alfdecapo/EGS_Modell/Bilder/Bodenadapter breit.png

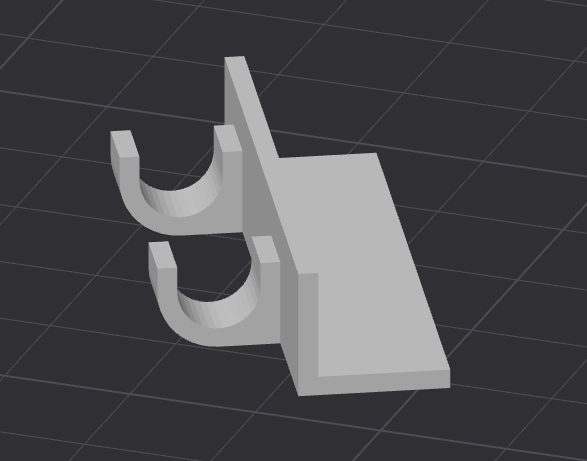
Bilder/Bodenadapter breit.png
