alfdecapo/EGS_Modell/Bilder/Demo_Längs.jpg

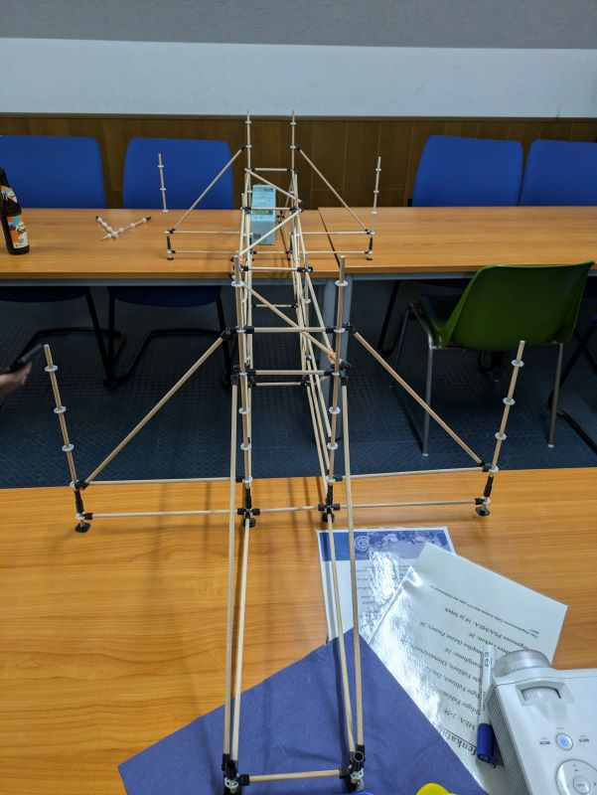
Bilder/Demo_Längs.jpg
