alfdecapo/EGS_Modell/Bilder/Demo_Seite.jpg

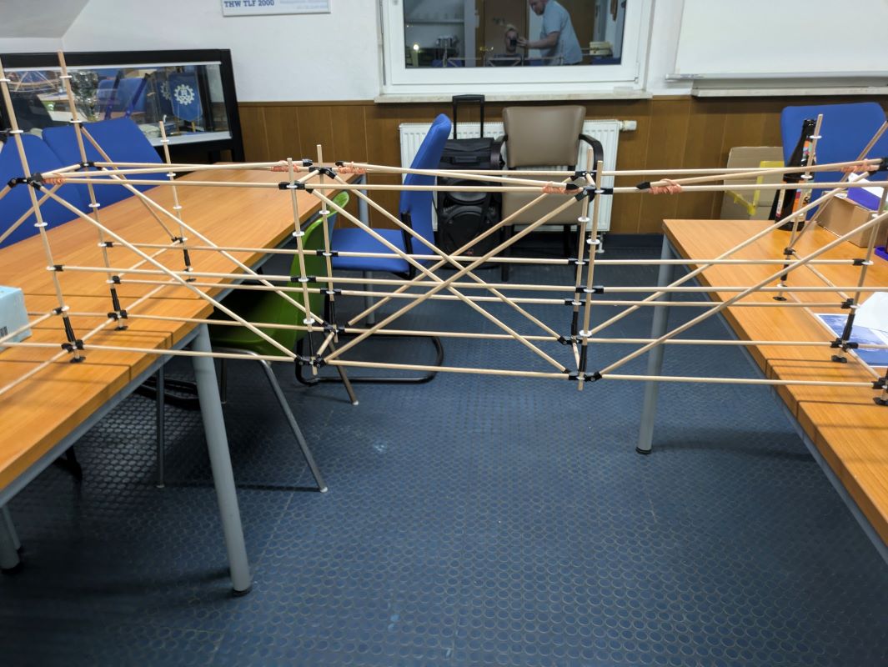
Bilder/Demo_Seite.jpg
