alfdecapo/EGS_Modell/Bilder/Vertikalschablone/Vertikalschablone_MitVertikalstielV2.jpg

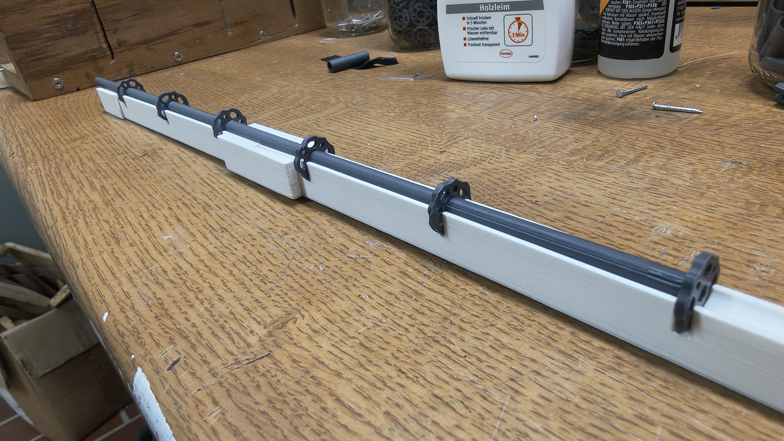
Bilder/Vertikalschablone/Vertikalschablone_MitVertikalstielV2.jpg
