alfdecapo/EGS_Modell/CAD Dateien/Teildruck 7.7/Diagonale Keilschloss.FCStd

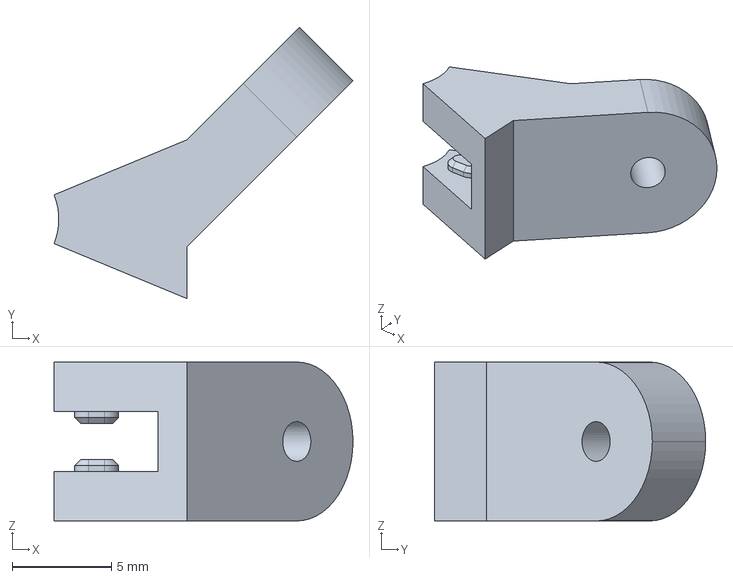
[picture p32: CAD file, 2026-05-11]
CAD Dateien/Teildruck 7.7/Diagonale Keilschloss.FCStd
15.0 x 13.7 x 8.00 mm
