alfdecapo/EGS_Modell/CAD Dateien/Teildruck 7.7/Ursprungsdateien Solid Works/Diagonale Gelenk.SLDPRT

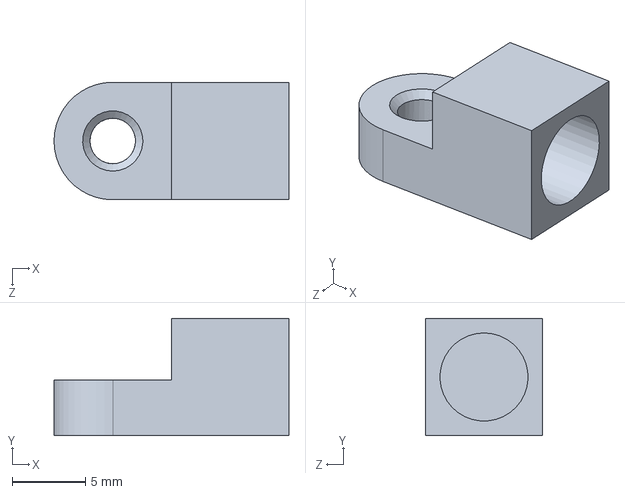
[picture p33: CAD file, 2026-04-20]
CAD Dateien/Teildruck 7.7/Ursprungsdateien Solid Works/Diagonale Gelenk.SLDPRT
16.0 x 8.00 x 8.00 mm
