alfdecapo/EGS_Modell/Drucker Dateien/Teildruck 7.7/Flansch 1zu7.7.STL

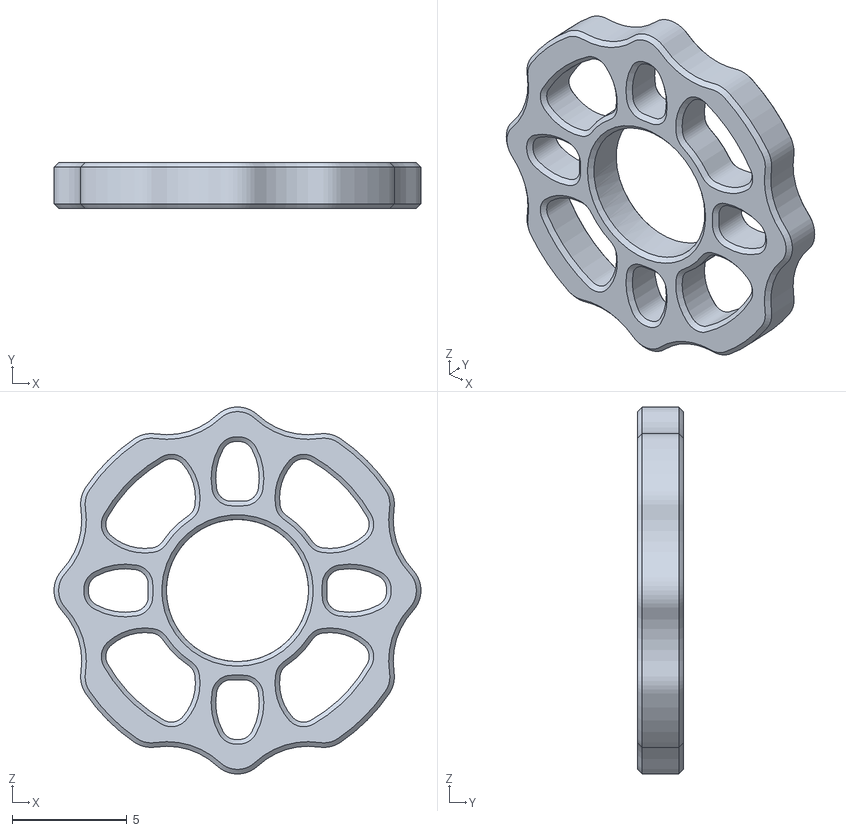
[picture p34: CAD file, 2026-04-20]
Drucker Dateien/Teildruck 7.7/Flansch 1zu7.7.STL
16.0 x 2.00 x 16.0
