alfdecapo/EGS_Modell/CAD Dateien/Teildruck 7.7/Flansch.FCStd

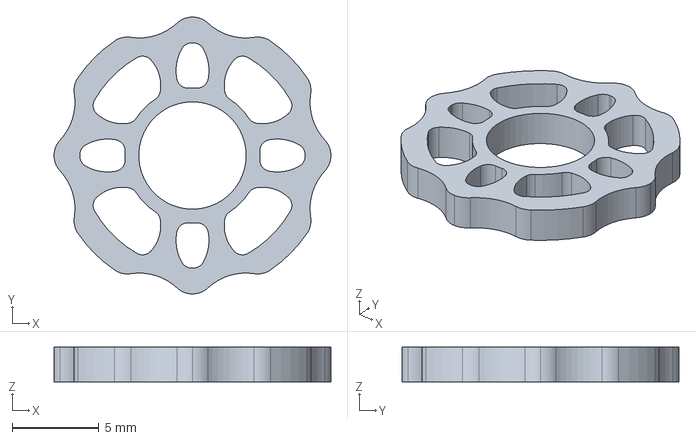
[picture p35: CAD file, 2026-05-11]
CAD Dateien/Teildruck 7.7/Flansch.FCStd
16.0 x 16.0 x 2.00 mm
