alfdecapo/EGS_Modell/Drucker Dateien/Teildruck 7.7/Fußadapter Simpel.STL

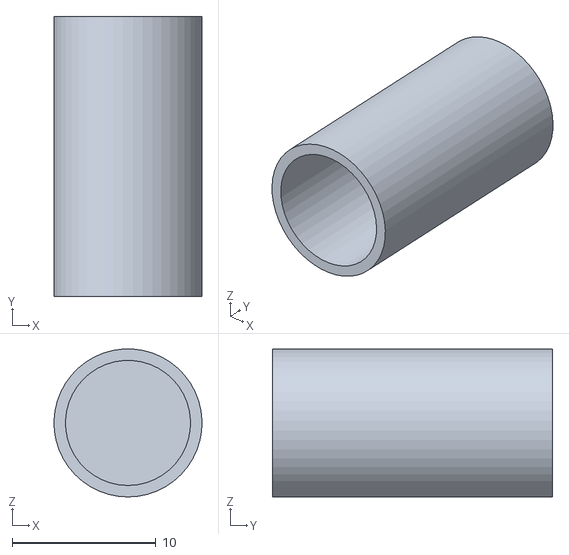
[picture p36: CAD file, 2026-04-20]
Drucker Dateien/Teildruck 7.7/Fußadapter Simpel.STL
10.3 x 19.5 x 10.3
