alfdecapo/EGS_Modell/Drucker Dateien/Teildruck 7.7/Flansch.STL

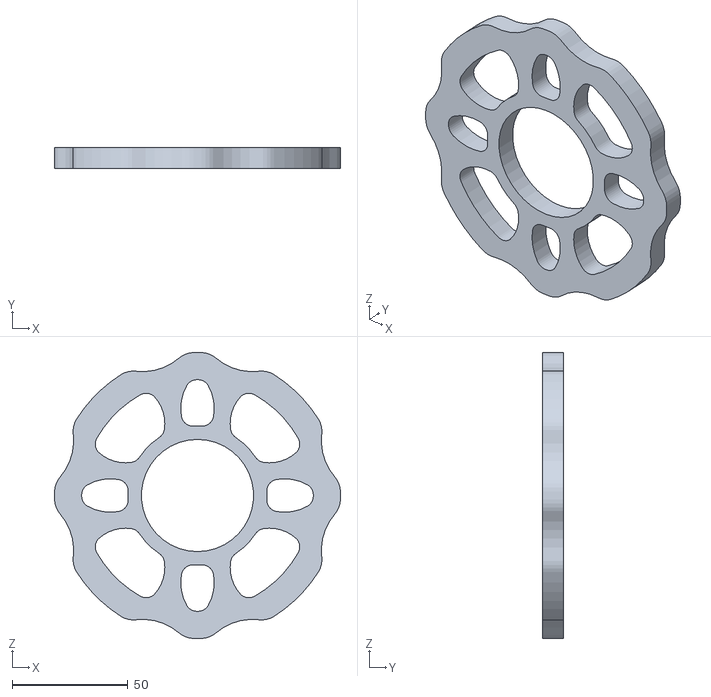
[picture p37: CAD file, 2026-04-20]
Drucker Dateien/Teildruck 7.7/Flansch.STL
123.5 x 9.00 x 123.5
