alfdecapo/EGS_Modell/CAD Dateien/Teildruck 7.7/Horizontale Keilschloss.FCStd

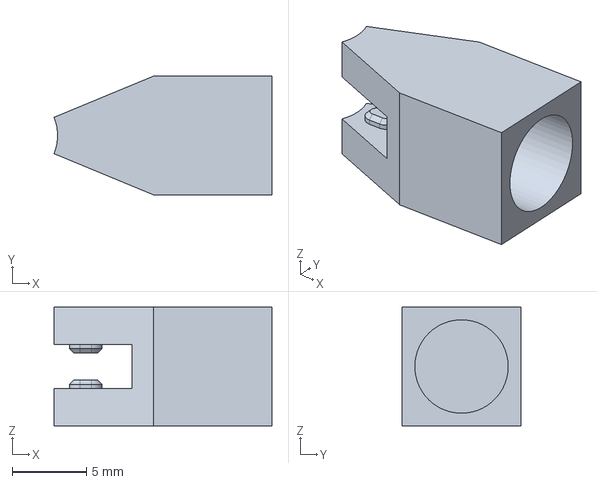
[picture p38: CAD file, 2026-05-11]
CAD Dateien/Teildruck 7.7/Horizontale Keilschloss.FCStd
14.7 x 8.00 x 8.00 mm
