alfdecapo/EGS_Modell/CAD Dateien/Teildruck 7.7/Vertikalen Verbinder.FCStd

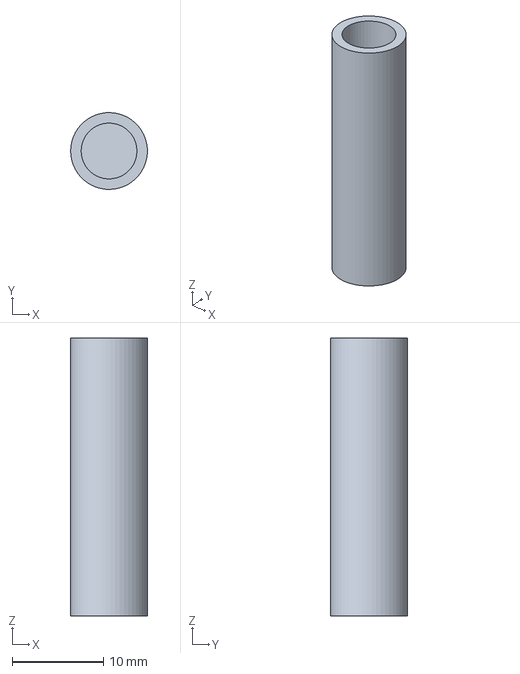
[picture p39: CAD file, 2026-05-11]
CAD Dateien/Teildruck 7.7/Vertikalen Verbinder.FCStd
8.39 x 8.40 x 30.4 mm
