alfdecapo/EGS_Modell/CAD Dateien/Teildruck 7.7/Ursprungsdateien Solid Works/Flansch 1zu7.7.SLDPRT

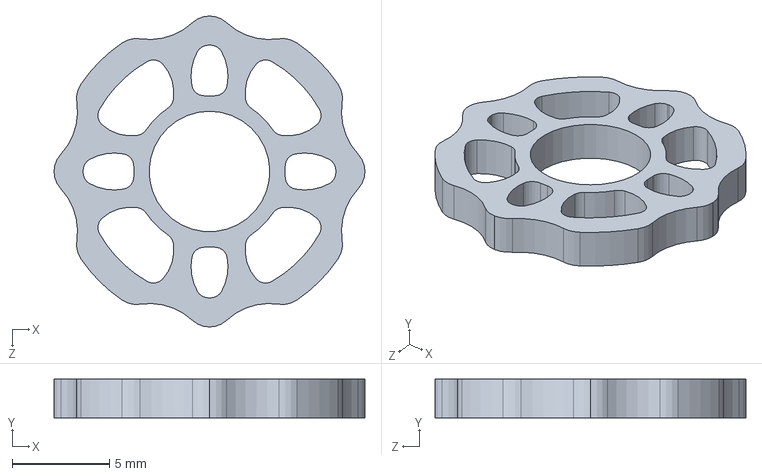
[picture p40: CAD file, 2026-04-20]
CAD Dateien/Teildruck 7.7/Ursprungsdateien Solid Works/Flansch 1zu7.7.SLDPRT
16.0 x 2.00 x 16.0 mm
