alfdecapo/EGS_Modell/CAD Dateien/Teildruck 7.7/Ursprungsdateien Solid Works/Flansch.SLDPRT

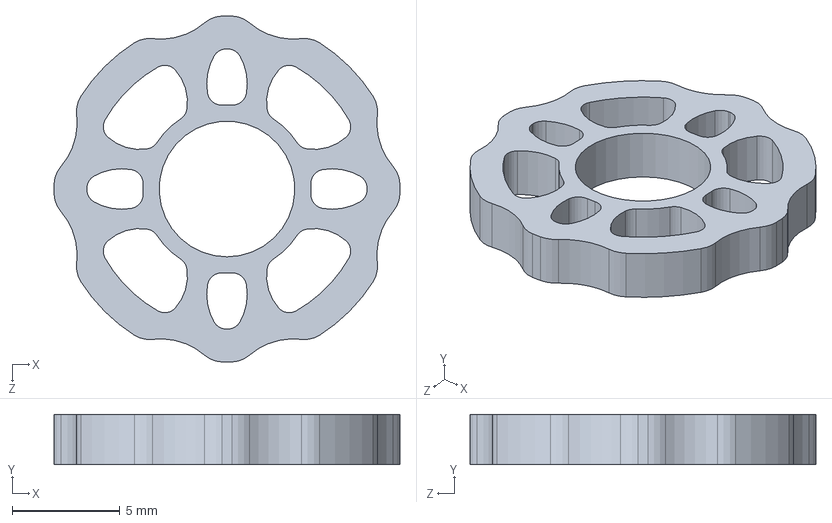
[picture p41: CAD file, 2026-04-20]
CAD Dateien/Teildruck 7.7/Ursprungsdateien Solid Works/Flansch.SLDPRT
16.0 x 2.34 x 16.0 mm
